Michelingumman/sauna-sensor-monitor/sauna-sensor-monitor/include/images.h

#ifndef IMAGES_H
#define IMAGES_H

static const unsigned char PROGMEM DROP_ICON[] = {0x04,0x00,0x04,0x00,0x0c,0x00,0x0a,0x00,0x12,0x00,0x11,0x00,0x20,0x80,0x20,0x80,0x41,0x40,0x40,0xc0,0x80,0xa0,0x80,0x20,0x40,0x40,0x40,0x40,0x30,0x80,0x0f,0x00};

static const unsigned char PROGMEM TEMP_ICON[] = {0x1c,0x00,0x22,0x02,0x2b,0x05,0x2a,0x02,0x2b,0x38,0x2a,0x60,0x2b,0x40,0x2a,0x40,0x2a,0x60,0x49,0x38,0x9c,0x80,0xae,0x80,0xbe,0x80,0x9c,0x80,0x41,0x00,0x3e,0x00};

static const unsigned char PROGMEM NO_NETWORK_ICON[] = {0x82,0x0e,0x44,0x0a,0x28,0x0a,0x10,0x0a,0x28,0xea,0x44,0xaa,0x82,0xaa,0x00,0xaa,0x0e,0xaa,0x0a,0xaa,0x0a,0xaa,0x0a,0xaa,0xea,0xaa,0xaa,0xaa,0xee,0xee,0x00,0x00};

#endif
